fmealing/Final-Year-Project/analytics/figures/fig1_imu_accel_magnitude.png

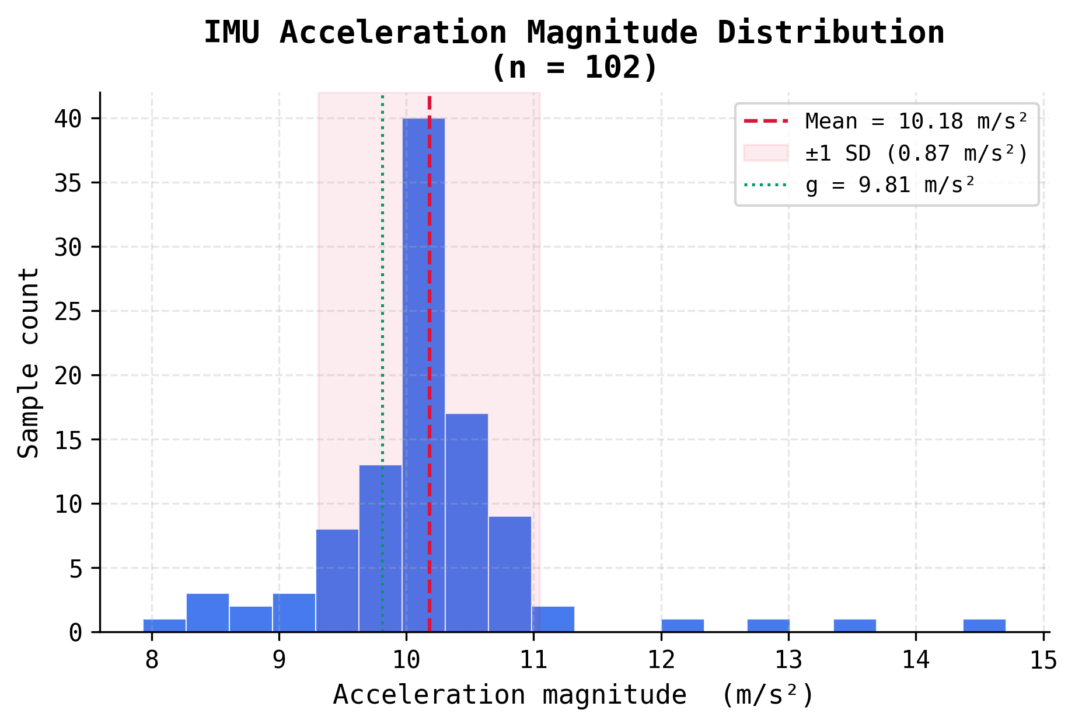
analytics/figures/fig1_imu_accel_magnitude.png
