fmealing/Final-Year-Project/analytics/figures/fig2_imu_timeseries.png

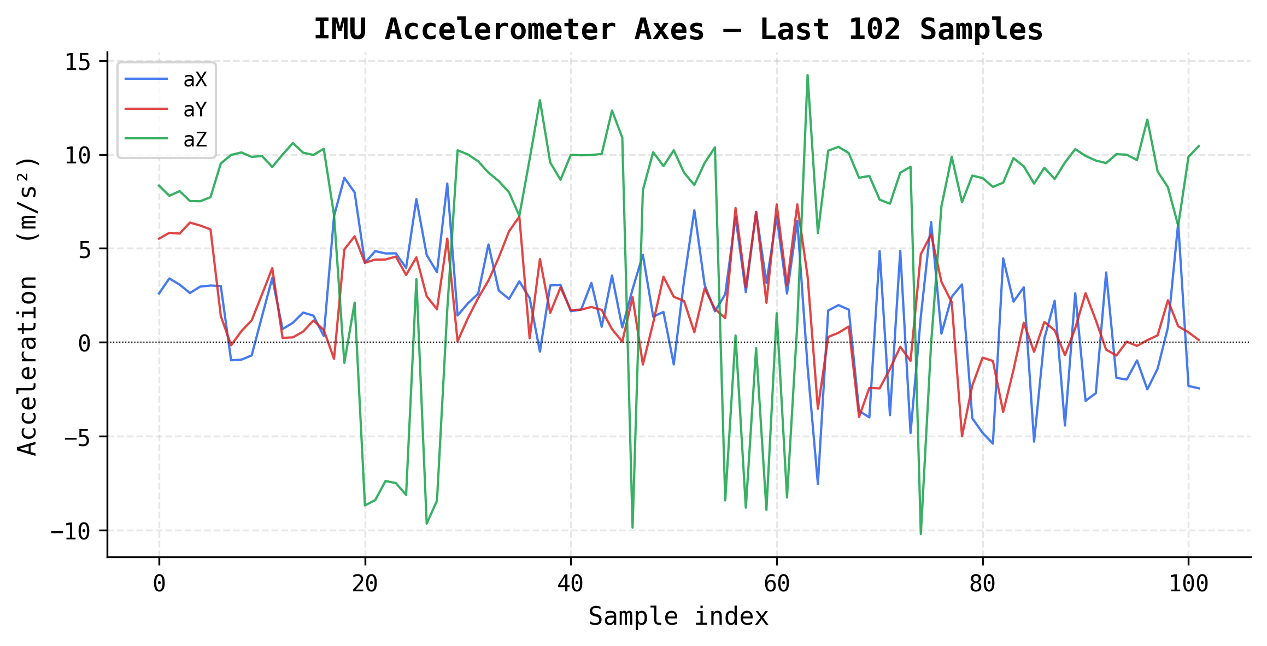
analytics/figures/fig2_imu_timeseries.png
