fmealing/Final-Year-Project/analytics/figures/fig4_accel_magnitude_timeseries.png

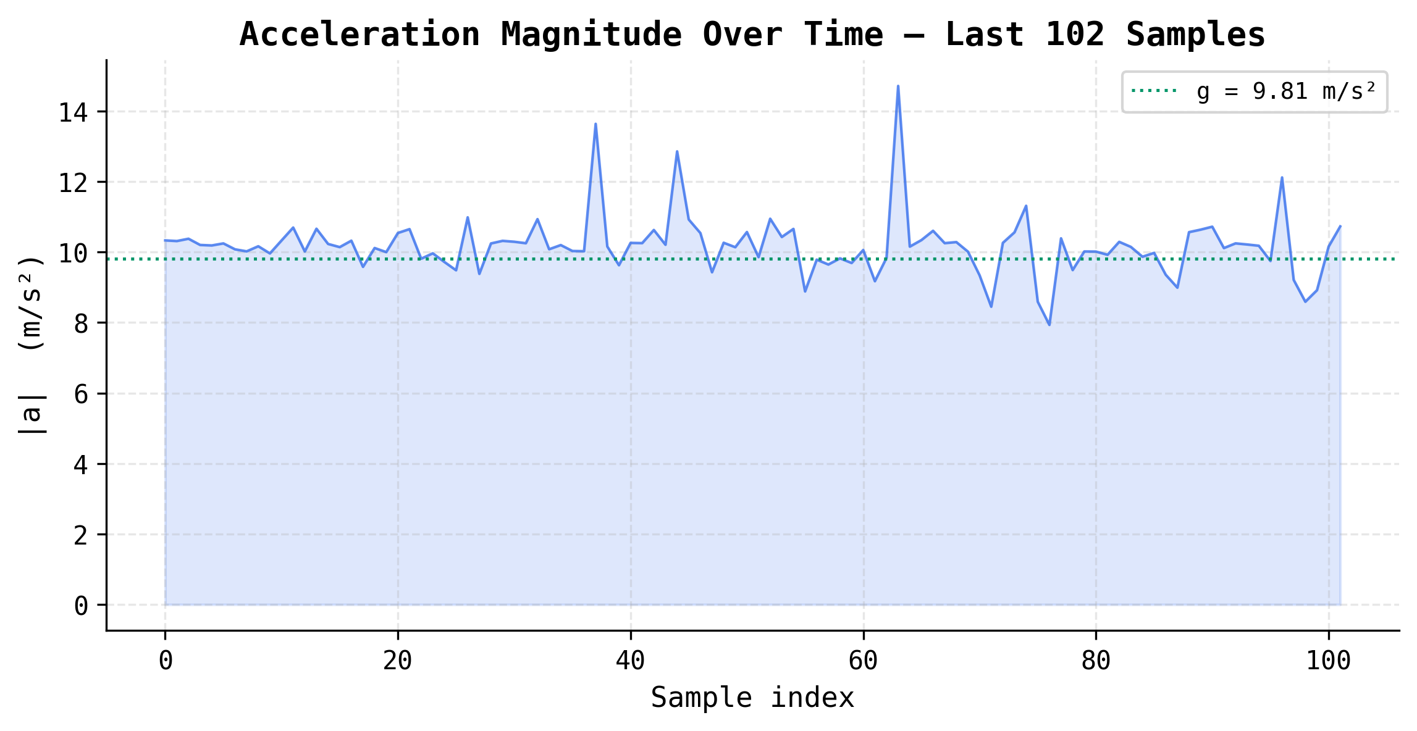
analytics/figures/fig4_accel_magnitude_timeseries.png
