fmealing/Final-Year-Project/images/cad.png

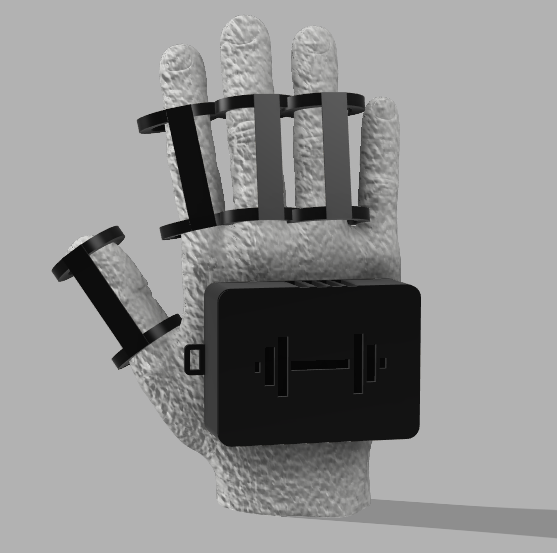
images/cad.png
