fmealing/Final-Year-Project/images/Glove_Sketch.PNG

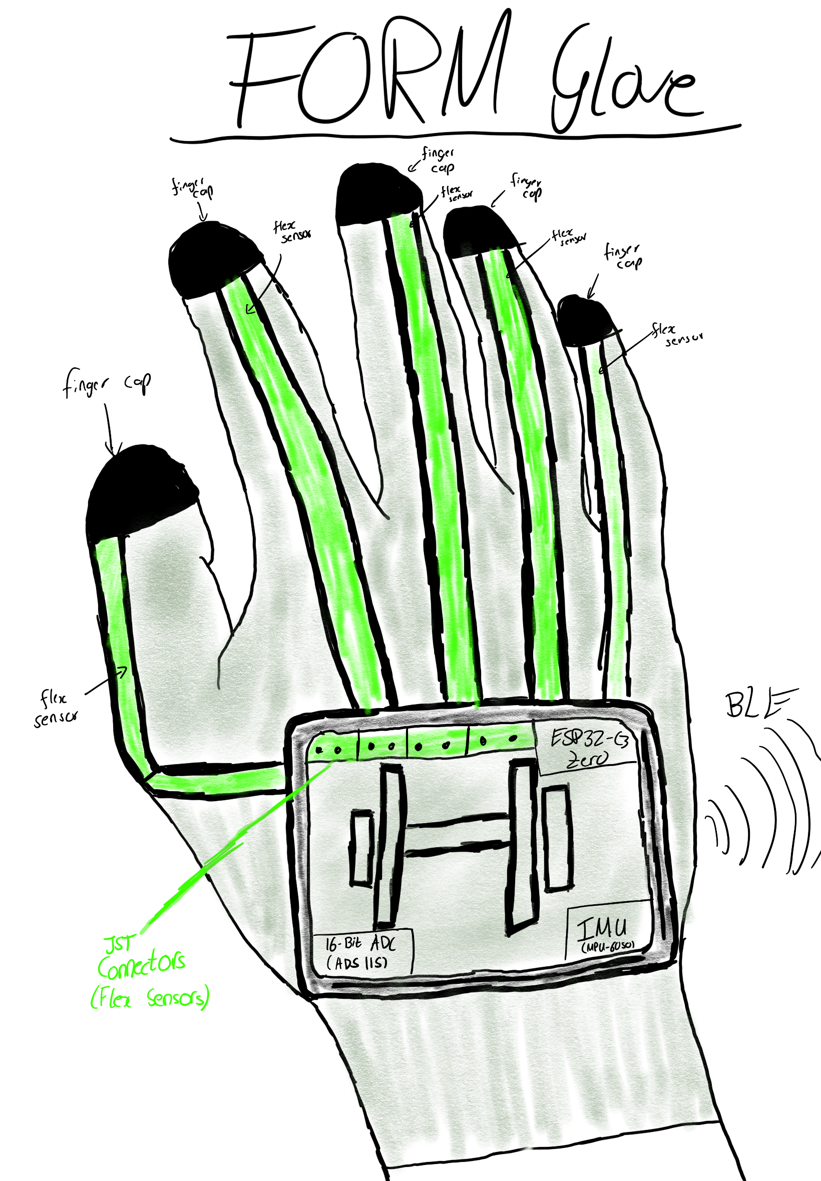
images/Glove_Sketch.PNG
