fmealing/Final-Year-Project/images/prototype3.png

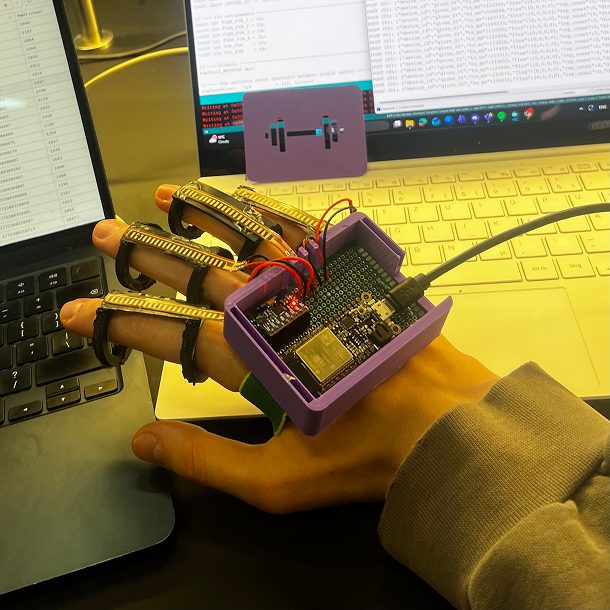
images/prototype3.png
