fmealing/Final-Year-Project/calibration/csv/1_flex_40_mm_tube.csv

# Ghost Glove Flex Calibration — 40 mm tube
t_s | flex_ring | flex_middle | flex_index | flex_thumb
0.046 | 4742 | 6266 | 3907 | 6601
0.046 | 4586 | 6110 | 3742 | 6583
0.102 | 4744 | 6245 | 3507 | 6514
0.144 | 4712 | 6355 | 3816 | 6582
0.161 | 4617 | 6251 | 3787 | 6637
0.192 | 4712 | 6192 | 3507 | 6563
0.242 | 4821 | 6339 | 3739 | 6558
0.251 | 4677 | 6183 | 3680 | 6660
0.281 | 4711 | 6239 | 3679 | 6580
0.343 | 4815 | 6313 | 3567 | 6546
0.372 | 4686 | 6335 | 3796 | 6609
0.403 | 4580 | 6144 | 3761 | 6600
0.462 | 4747 | 6282 | 3531 | 6525
0.463 | 4728 | 6353 | 3723 | 6589
0.492 | 4598 | 6231 | 3726 | 6626
0.521 | 4682 | 6248 | 3577 | 6564
0.582 | 4835 | 6316 | 3651 | 6576
0.612 | 4684 | 6236 | 3810 | 6663
0.644 | 4683 | 6143 | 3692 | 6596
0.673 | 4804 | 6321 | 3515 | 6529
0.701 | 4698 | 6264 | 3850 | 6607
0.731 | 4583 | 6185 | 3727 | 6578
0.762 | 4732 | 6240 | 3615 | 6506
0.792 | 4724 | 6301 | 3816 | 6582
0.882 | 4596 | 6404 | 3777 | 6634
0.883 | 4710 | 6361 | 3599 | 6574
0.912 | 4819 | 6317 | 3740 | 6598
0.942 | 4699 | 6225 | 3858 | 6659
0.972 | 4678 | 5912 | 3640 | 6594
1.002 | 4808 | 6176 | 3757 | 6553
1.031 | 4705 | 6229 | 3964 | 6612
1.092 | 4588 | 6203 | 3774 | 6589
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
