fmealing/Final-Year-Project/calibration/csv/1_flex_50_mm_tube.csv

# Ghost Glove Flex Calibration — 50 mm tube
t_s | flex_ring | flex_middle | flex_index | flex_thumb
0.011 | 4715 | 6721 | 3956 | 6134
0.037 | 4550 | 6634 | 3634 | 6129
0.098 | 4697 | 6701 | 3747 | 6038
0.099 | 4709 | 6815 | 3805 | 6126
0.128 | 4571 | 6693 | 3834 | 6171
0.161 | 4655 | 6671 | 3440 | 6109
0.228 | 4825 | 6765 | 3785 | 6123
0.248 | 4663 | 6727 | 3879 | 6192
0.278 | 4672 | 6591 | 3749 | 6138
0.308 | 4764 | 6698 | 3798 | 6058
0.337 | 4684 | 6734 | 4018 | 6145
0.368 | 4529 | 6659 | 3826 | 6135
0.429 | 4681 | 6682 | 3535 | 6050
0.472 | 4697 | 6805 | 3774 | 6154
0.487 | 4580 | 6714 | 3716 | 6202
0.547 | 4683 | 6623 | 3572 | 6125
0.548 | 4837 | 6740 | 3767 | 6127
0.577 | 4672 | 6717 | 3914 | 6201
0.608 | 4659 | 6587 | 3706 | 6148
0.670 | 4748 | 6692 | 3733 | 6061
0.670 | 4701 | 6751 | 3934 | 6157
0.728 | 4518 | 6672 | 3739 | 6157
0.758 | 4676 | 6687 | 3569 | 6094
0.788 | 4772 | 6816 | 3786 | 6149
0.878 | 4611 | 6722 | 3783 | 6211
0.880 | 4678 | 6648 | 3574 | 6131
0.880 | 4838 | 6738 | 3739 | 6118
0.909 | 4651 | 6715 | 3965 | 6208
0.968 | 4592 | 6592 | 3735 | 6159
0.998 | 4674 | 6596 | 3680 | 6156
1.028 | 4772 | 6700 | 3750 | 6084
1.057 | 4702 | 6707 | 3966 | 6174
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
