fmealing/Final-Year-Project/calibration/csv/1_flex_fist.csv

# Ghost Glove Flex Calibration — Fist
t_s | flex_ring | flex_middle | flex_index | flex_thumb
0.013 | 4497 | 6326 | 3282 | 4932
0.073 | 4507 | 6254 | 3492 | 5016
0.075 | 4381 | 6224 | 3281 | 5040
0.104 | 4472 | 6183 | 3362 | 4967
0.164 | 4519 | 6255 | 3461 | 5015
0.193 | 4457 | 6165 | 3454 | 5105
0.226 | 4468 | 6217 | 3206 | 5015
0.253 | 4597 | 6284 | 3439 | 4999
0.283 | 4497 | 6272 | 3425 | 5081
0.314 | 4457 | 6237 | 3302 | 5023
0.344 | 4522 | 6286 | 3336 | 4945
0.407 | 4500 | 6384 | 3493 | 5029
0.436 | 4387 | 6199 | 3379 | 5039
0.464 | 4475 | 6246 | 3203 | 4952
0.495 | 4522 | 6256 | 3325 | 5026
0.526 | 4432 | 6338 | 3348 | 5073
0.554 | 4476 | 6251 | 3219 | 5008
0.584 | 4593 | 6204 | 3305 | 5005
0.647 | 4494 | 6175 | 3380 | 5107
0.674 | 4461 | 6182 | 3297 | 5021
0.704 | 4553 | 6317 | 3341 | 4974
0.764 | 4499 | 6254 | 3464 | 5041
0.764 | 4502 | 6314 | 3457 | 5084
0.795 | 4462 | 6222 | 3362 | 5027
0.827 | 4522 | 6327 | 3368 | 4943
0.884 | 4501 | 6351 | 3428 | 5034
0.920 | 4387 | 6358 | 3327 | 5043
0.943 | 4498 | 6333 | 3230 | 4958
1.004 | 4533 | 6371 | 3423 | 5016
1.004 | 4443 | 6319 | 3421 | 5074
1.033 | 4474 | 6238 | 3268 | 4995
1.124 | 4592 | 6229 | 3250 | 5000
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
